imoralesgt/WSN_ICTP/KiCAD/Gateway/preview/back01.jpg

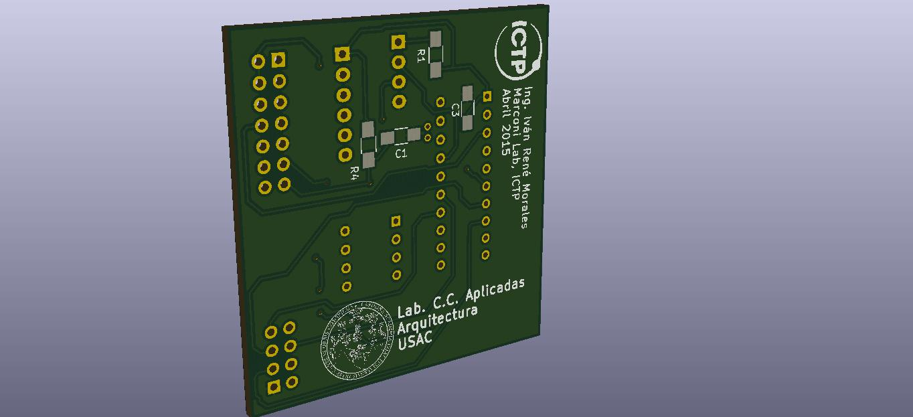
KiCAD/Gateway/preview/back01.jpg
