imoralesgt/WSN_ICTP/KiCAD/Gateway/preview/back02.jpg

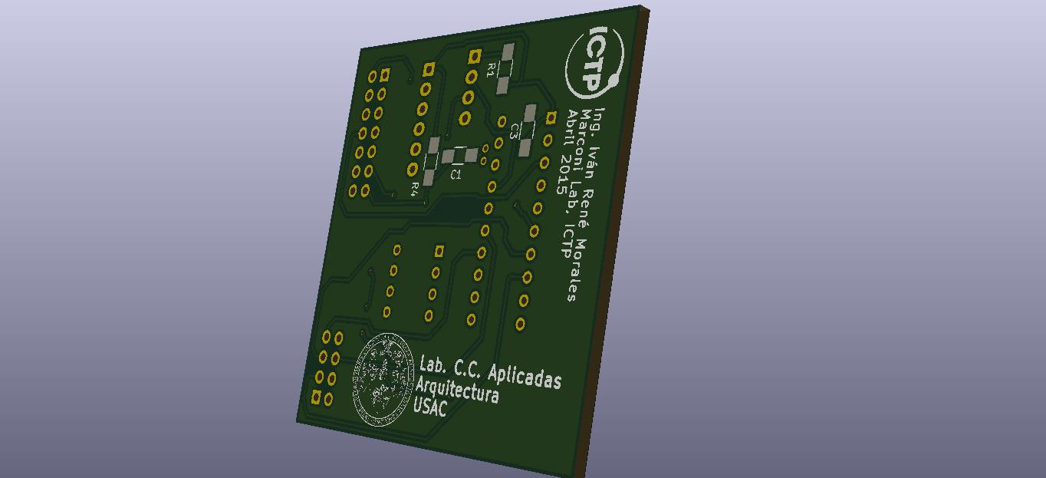
KiCAD/Gateway/preview/back02.jpg
