imoralesgt/WSN_ICTP/RouterRPi/exositeTest.py

## python_helloworld.py
## Tested with python 2.6.5
##
## Copyright (c) 2011, Exosite LLC
## All rights reserved.
##
## Redistribution and use in source and binary forms, with or without 
## modification, are permitted provided that the following conditions are met:
##
##    * Redistributions of source code must retain the above copyright notice,
##      this list of conditions and the following disclaimer.
##    * Redistributions in binary form must reproduce the above copyright 
##      notice, this list of conditions and the following disclaimer in the
##      documentation and/or other materials provided with the distribution.
##    * Neither the name of Exosite LLC nor the names of its contributors may
##      be used to endorse or promote products derived from this software 
##      without specific prior written permission.
##
## THIS SOFTWARE IS PROVIDED BY THE COPYRIGHT HOLDERS AND CONTRIBUTORS "AS IS"
## AND ANY EXPRESS OR IMPLIED WARRANTIES, INCLUDING, BUT NOT LIMITED TO, THE 
## IMPLIED WARRANTIES OF MERCHANTABILITY AND FITNESS FOR A PARTICULAR PURPOSE
## ARE DISCLAIMED. IN NO EVENT SHALL THE COPYRIGHT HOLDER OR CONTRIBUTORS BE 
## LIABLE FOR ANY DIRECT, INDIRECT, INCIDENTAL, SPECIAL, EXEMPLARY, OR 
## CONSEQUENTIAL DAMAGES (INCLUDING, BUT NOT LIMITED TO, PROCUREMENT OF 
## SUBSTITUTE GOODS OR SERVICES; LOSS OF USE, DATA, OR PROFITS; OR BUSINESS
## INTERRUPTION) HOWEVER CAUSED AND ON ANY THEORY OF LIABILITY, WHETHER IN 
## CONTRACT, STRICT LIABILITY, OR TORT (INCLUDING NEGLIGENCE OR OTHERWISE) 
## ARISING IN ANY WAY OUT OF THE USE OF THIS SOFTWARE, EVEN IF ADVISED OF THE
## POSSIBILITY OF SUCH DAMAGE.
""" 
  Exosite HTTP POST/GET REST API example (HELLO WORLD!)
"""

""" 
  Directions:
  1) Have an Exosite Portals account
  2) Add a new Device client to your portal.  Click on it to get it's CIK (KEY)
  3) Add the CIK below where it says 'PUTYOURCIKHERE'. (inside of the quotes)
  4) On your portal, add two data sources.  This script does not auto-create the data sources.
      Data Source 1 should be called 'message', type is string, resource is 'message'
      Data Source 2 should be called 'number', type is integer, resource is 'number'
  5) Run this python script in Python 2.6.5 or higher.
  6) Assuming your computer has an active network connection, you should see data sent to
      these data sources on your portal.  The script runs only once.  It should also print out
      what it sent, since it is doing a 'read' after the 'write'.
  
"""

import urllib 
import httplib
import time
import math

cik = '83c7008383e15f4c8648bb4704f625bf30b33188'

server = 'm2.exosite.com'



print '========================================================================'
print 'REST API DEMO. Using CIK ', cik
print '========================================================================'
print '\r\n'

j = 0
i = int((math.sin(j/100.0)+0.5)*256)

while True:
    i = int((math.sin(j/100.0)+0.5)*256)
    url = '/api:v1/stack/alias' 
    params = urllib.urlencode({'message': 'ola ke ase!', 'number': i })
    headers = {'X-Exosite-CIK': cik, 'content-type': 'application/x-www-form-urlencoded; charset=utf-8'} 
    print '=================='
    print 'POST'
    print '=================='
    print 'URL: ', url
    print 'Data: ', params
    print ' '
    conn = httplib.HTTPConnection(server) 
    conn.set_debuglevel(1)
    conn.request("POST",url,params,headers) 
    response = conn.getresponse(); 
    print 'response: ',response.status,response.reason 
    data = response.read() 
    end = data.find('<')
    if -1 == end: end = len(data)

    print '\r\n\r\n'
    url = '/api:v1/stack/alias?message&number'
    headers = {'Accept':'application/x-www-form-urlencoded; charset=utf-8','X-Exosite-CIK':cik}
    print '=================='
    print 'GET'
    print '=================='  
    print 'URL: ', url
    print ' '

    conn = httplib.HTTPConnection(server)
    conn.request("GET",url,"",headers)
    response = conn.getresponse();
    print 'response: ',response.status,response.reason
    data = response.read()
    conn.close()
    print 'response data:', data


    conn.close()

    j += 1
